adrirubio/odins-eye/demo/POC-pictures/POC4.jpg

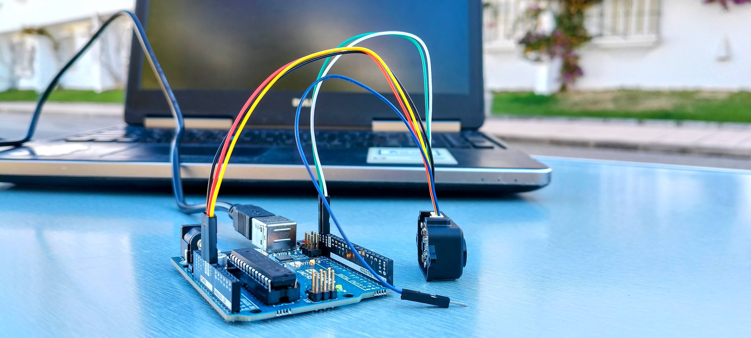
demo/POC-pictures/POC4.jpg
