adrirubio/odins-eye/demo/POC-pictures/POC.jpeg

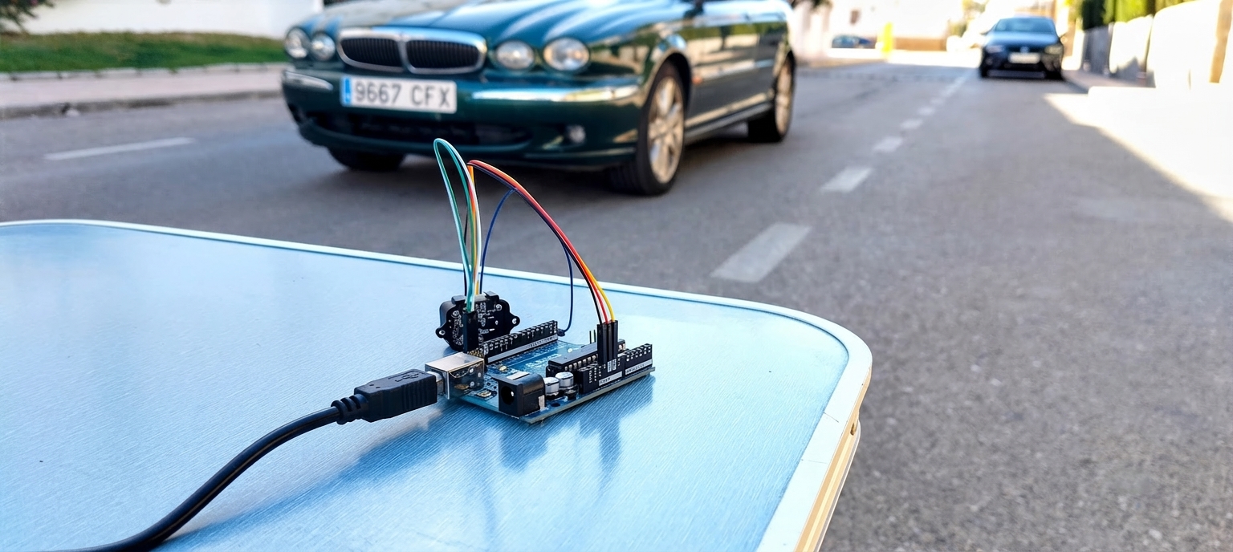
demo/POC-pictures/POC.jpeg
